ShivamASNS-py/ASNS/images/2pin_JST_connectors.jpg

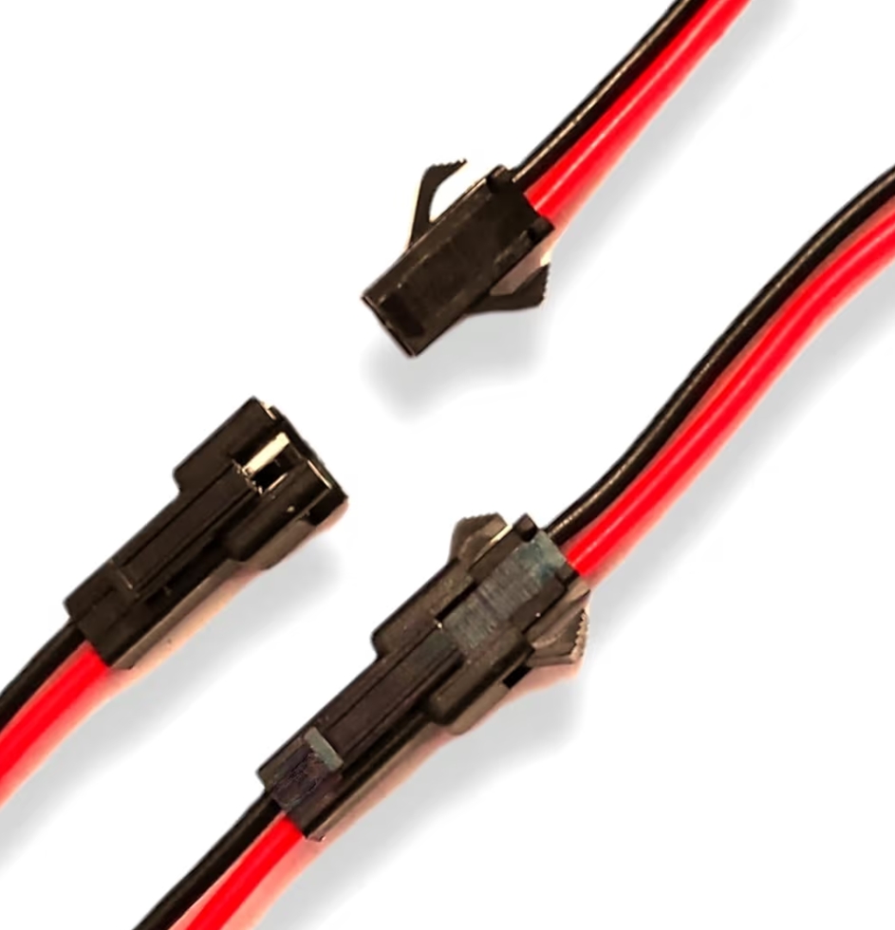
images/2pin_JST_connectors.jpg
