ShivamASNS-py/ASNS/images/18AWG_wires.jpg

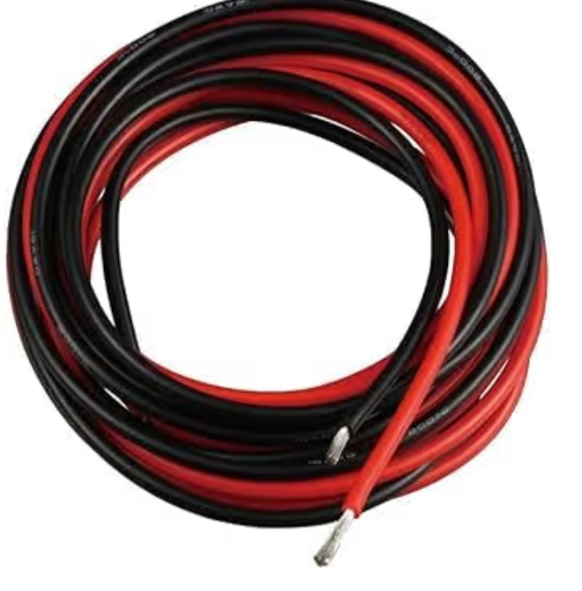
images/18AWG_wires.jpg
