ShivamASNS-py/ASNS/images/26AWG_wires.jpg

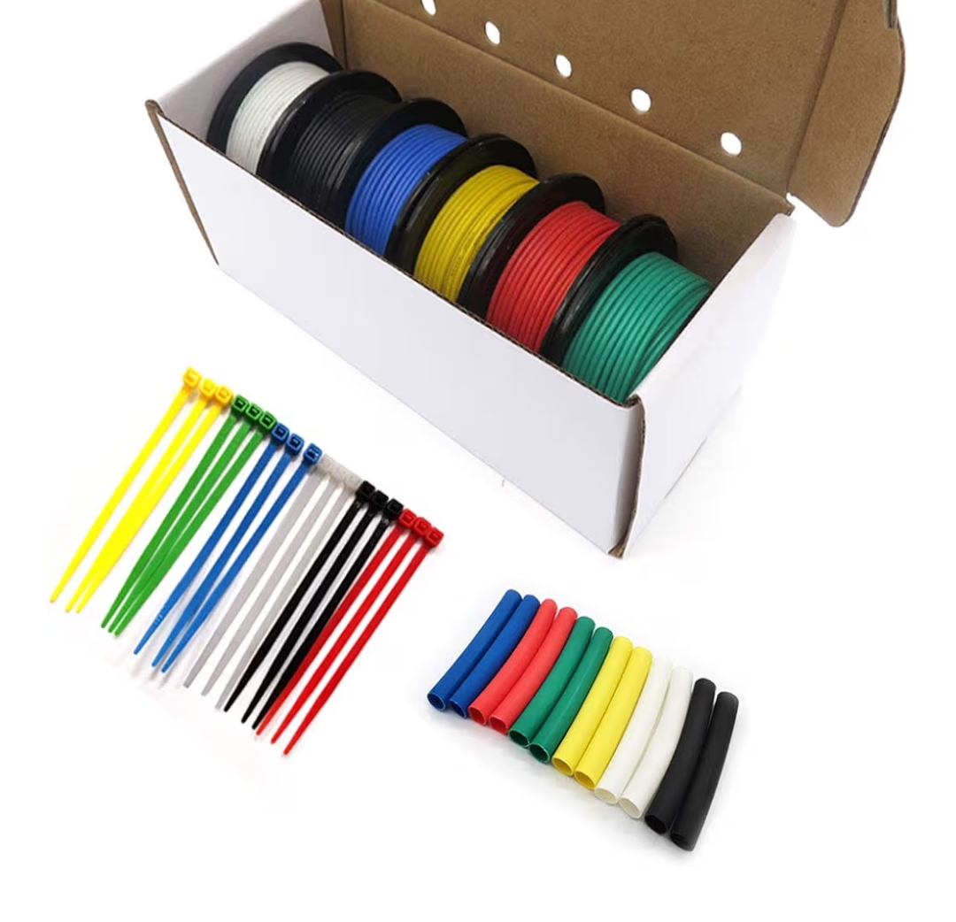
images/26AWG_wires.jpg
