ShivamASNS-py/ASNS/images/Capacitors.jpg

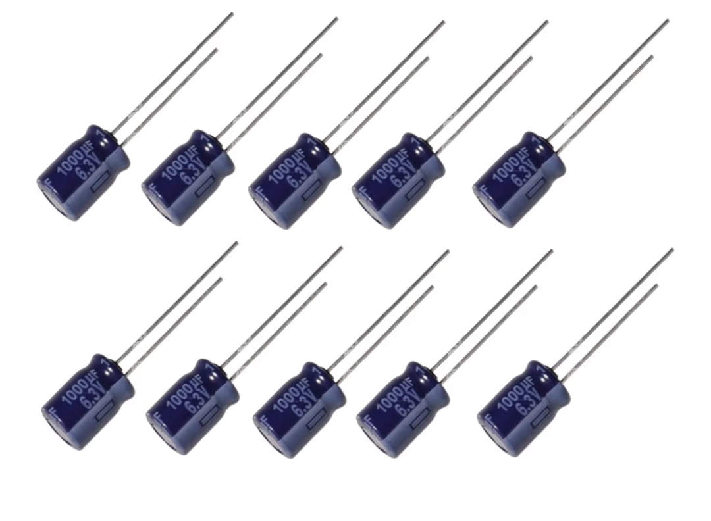
images/Capacitors.jpg
