ShivamASNS-py/ASNS/images/Double_sided_tape.jpg

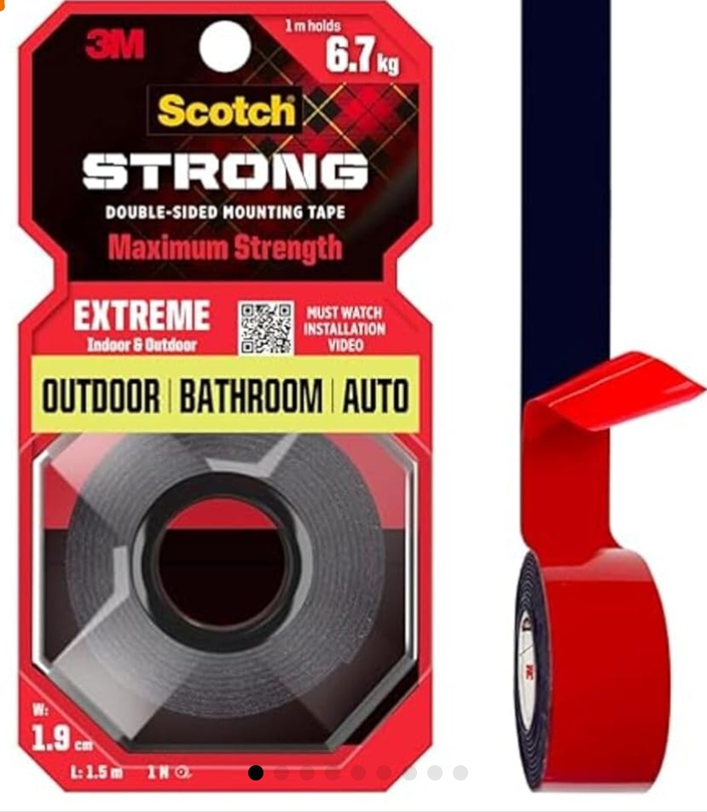
images/Double_sided_tape.jpg
