ShivamASNS-py/ASNS/images/ESP32-WROVER-IE.jpg

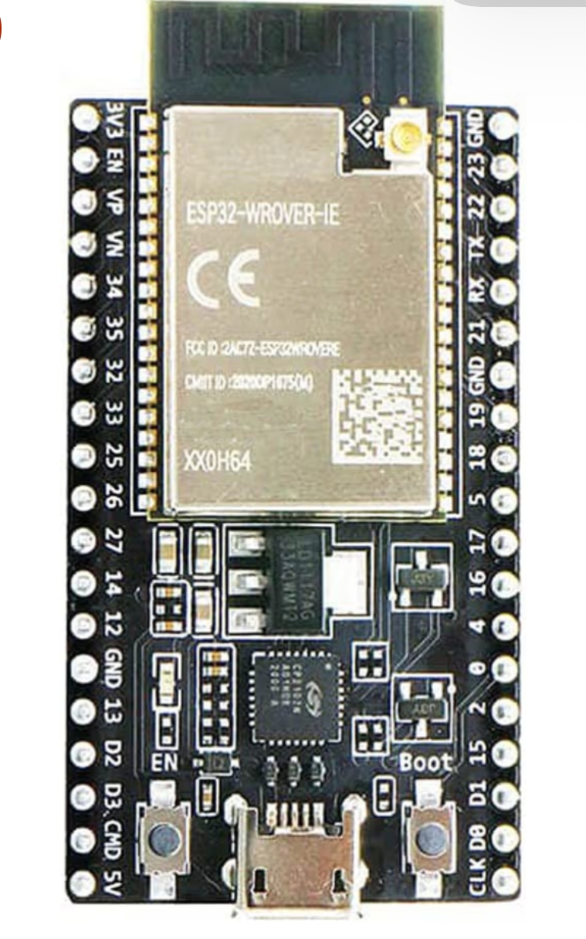
images/ESP32-WROVER-IE.jpg
