ShivamASNS-py/ASNS/images/Female_DC_Connectors.jpg

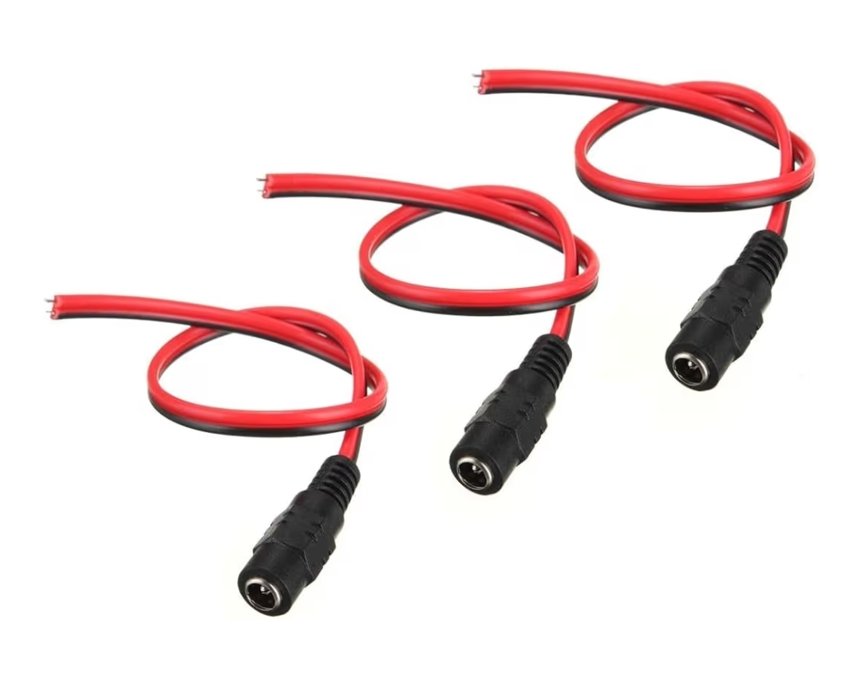
images/Female_DC_Connectors.jpg
