ShivamASNS-py/ASNS/images/Logic level shifters.jpg

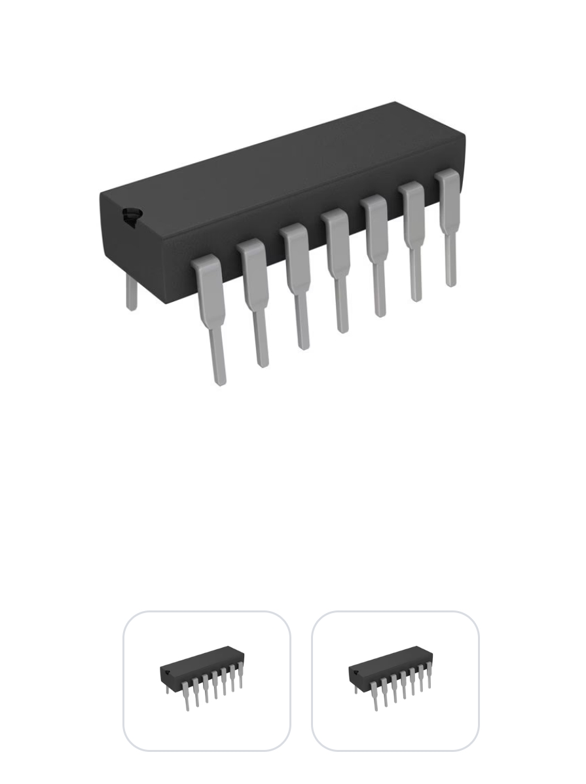
images/Logic level shifters.jpg
