ShivamASNS-py/ASNS/images/Mini buck.jpg

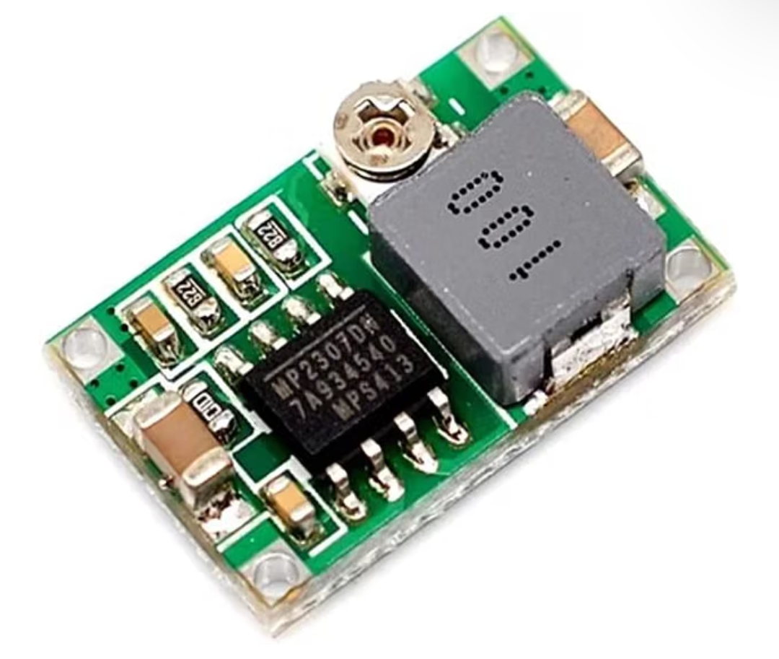
images/Mini buck.jpg
