ShivamASNS-py/ASNS/images/Perfboard.jpg

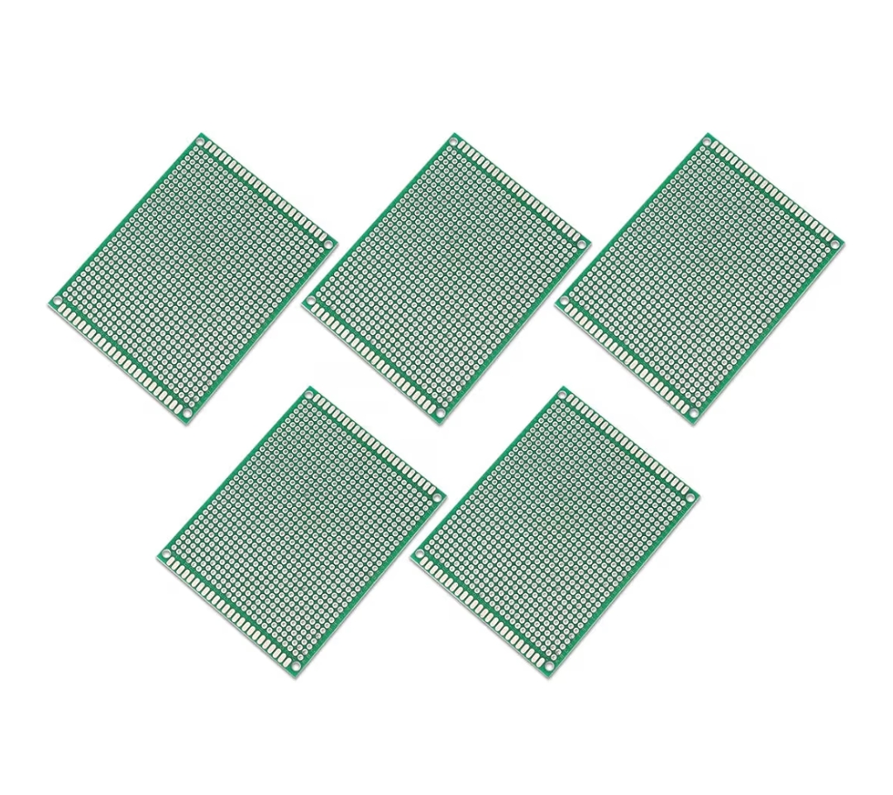
images/Perfboard.jpg
