ShivamASNS-py/ASNS/images/Resistor's 330 ohms.jpg

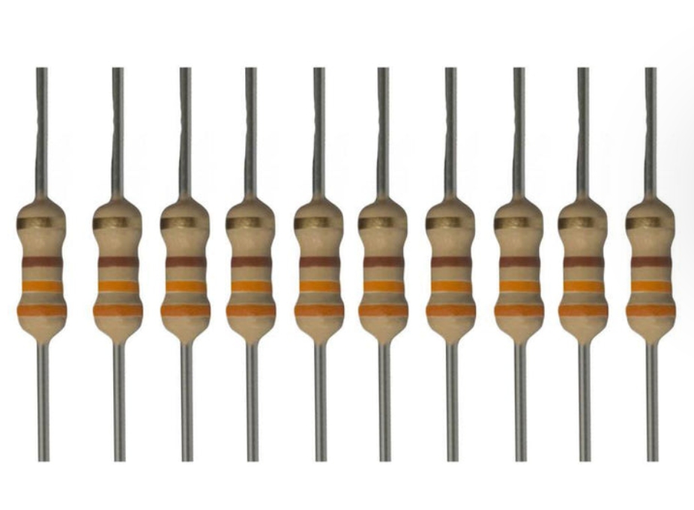
images/Resistor's 330 ohms.jpg
