ShivamASNS-py/ASNS/images/screws.jpg

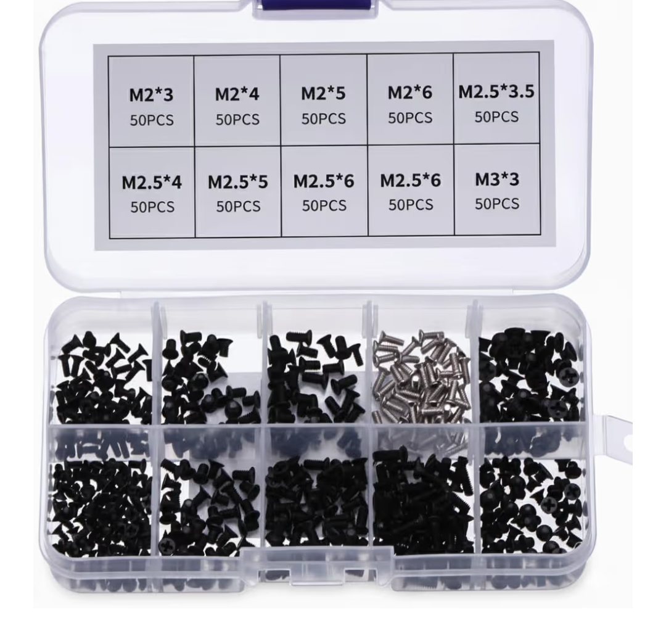
images/screws.jpg
