ShivamASNS-py/ASNS/images/SMPS.jpg

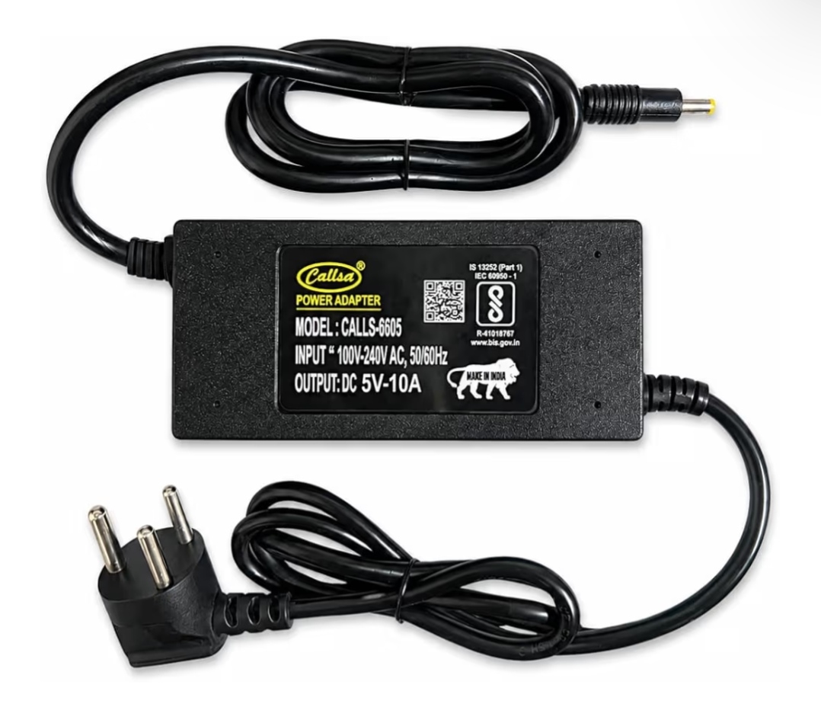
images/SMPS.jpg
