ShivamASNS-py/ASNS/images/TFT_SPI_PANEL.jpg

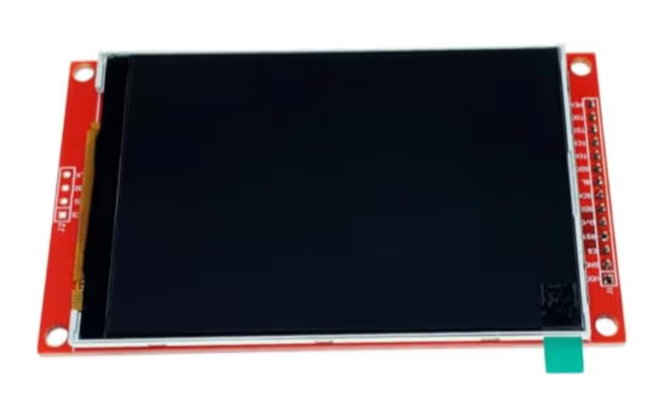
images/TFT_SPI_PANEL.jpg
