ShivamASNS-py/ASNS/images/TTP223 touch pads.jpeg

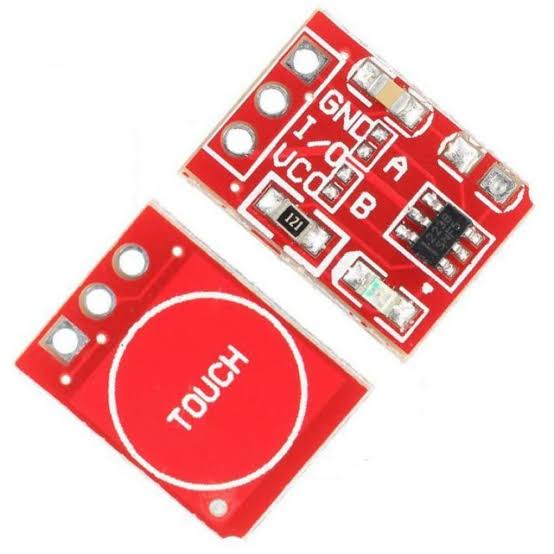
images/TTP223 touch pads.jpeg
