ShivamASNS-py/ASNS/images/Waveshare IPS Display.jpg

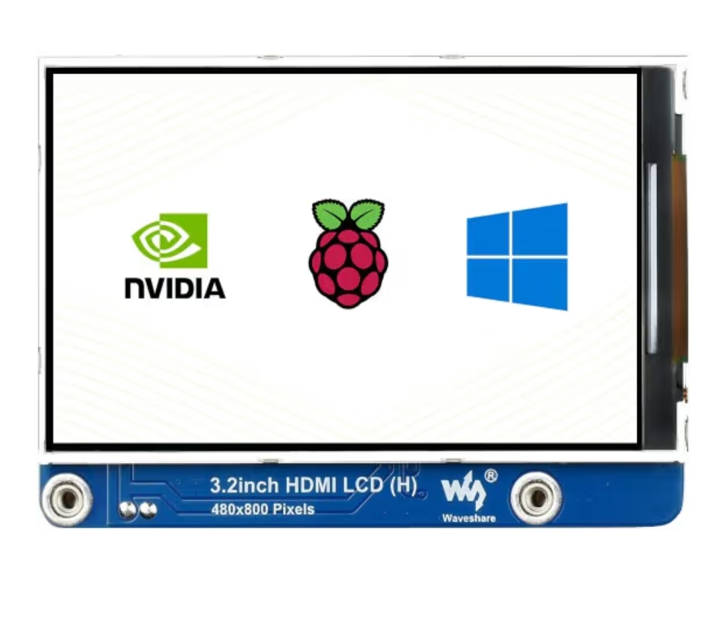
images/Waveshare IPS Display.jpg
