ShivamASNS-py/ASNS/images/WS2812B.jpg

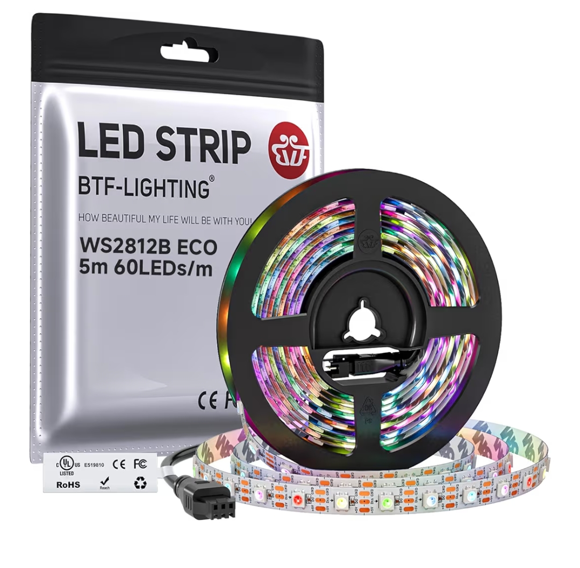
images/WS2812B.jpg
