ShivamASNS-py/ASNS/Hardware/Wiring Diagram.png

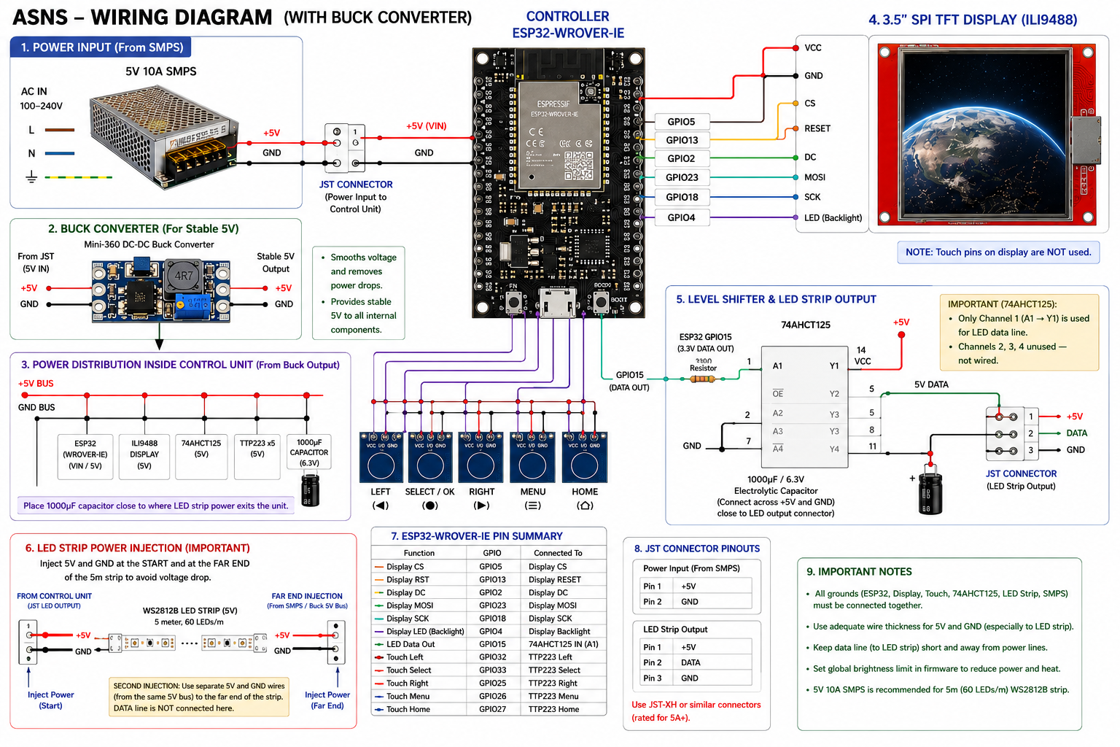
Hardware/Wiring Diagram.png
